Jaycar-Electronics/WiFi-Mains-Switch/images/aio/rydalmere.PNG

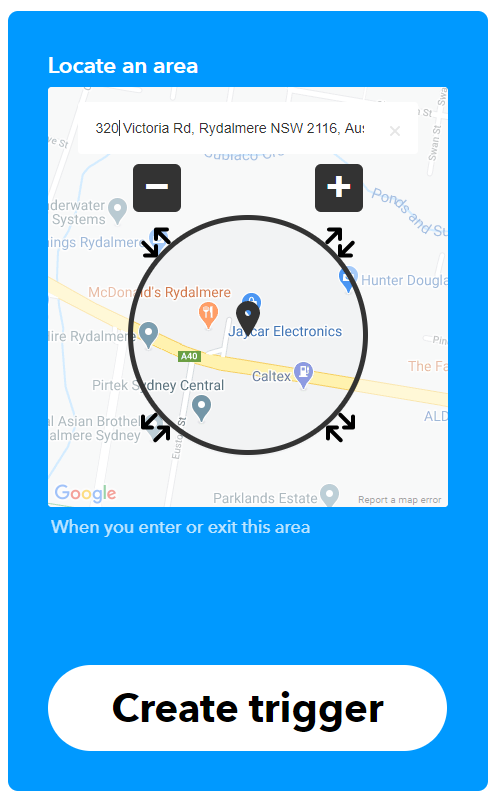
images/aio/rydalmere.PNG
