Jaycar-Electronics/WiFi-Mains-Switch/images/IMAG1999.jpg

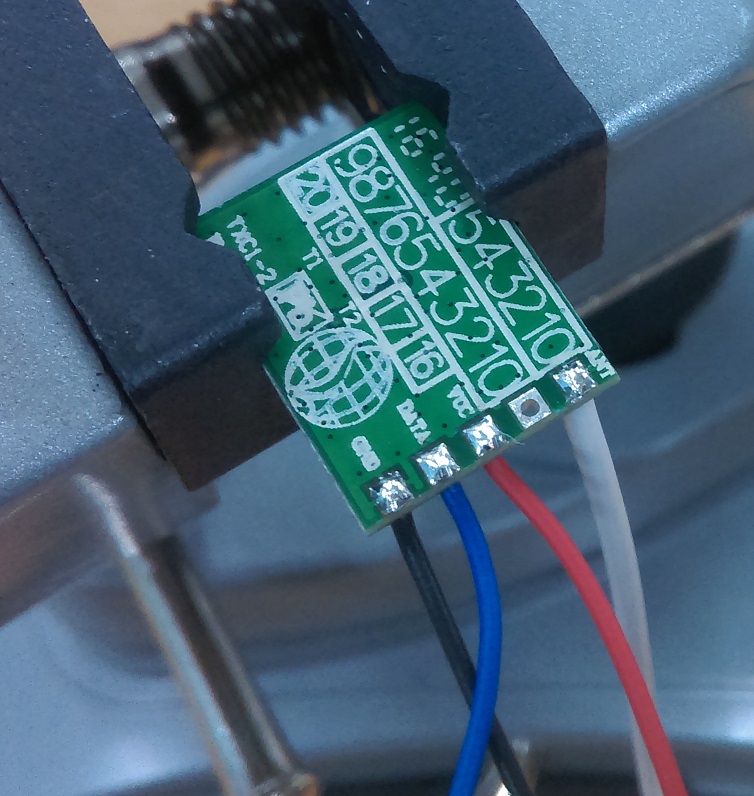
images/IMAG1999.jpg
